Harishanan/Machine-Learning-HPC-/CreateManPage/Screenshot from 2024-03-30 01-08-20.png

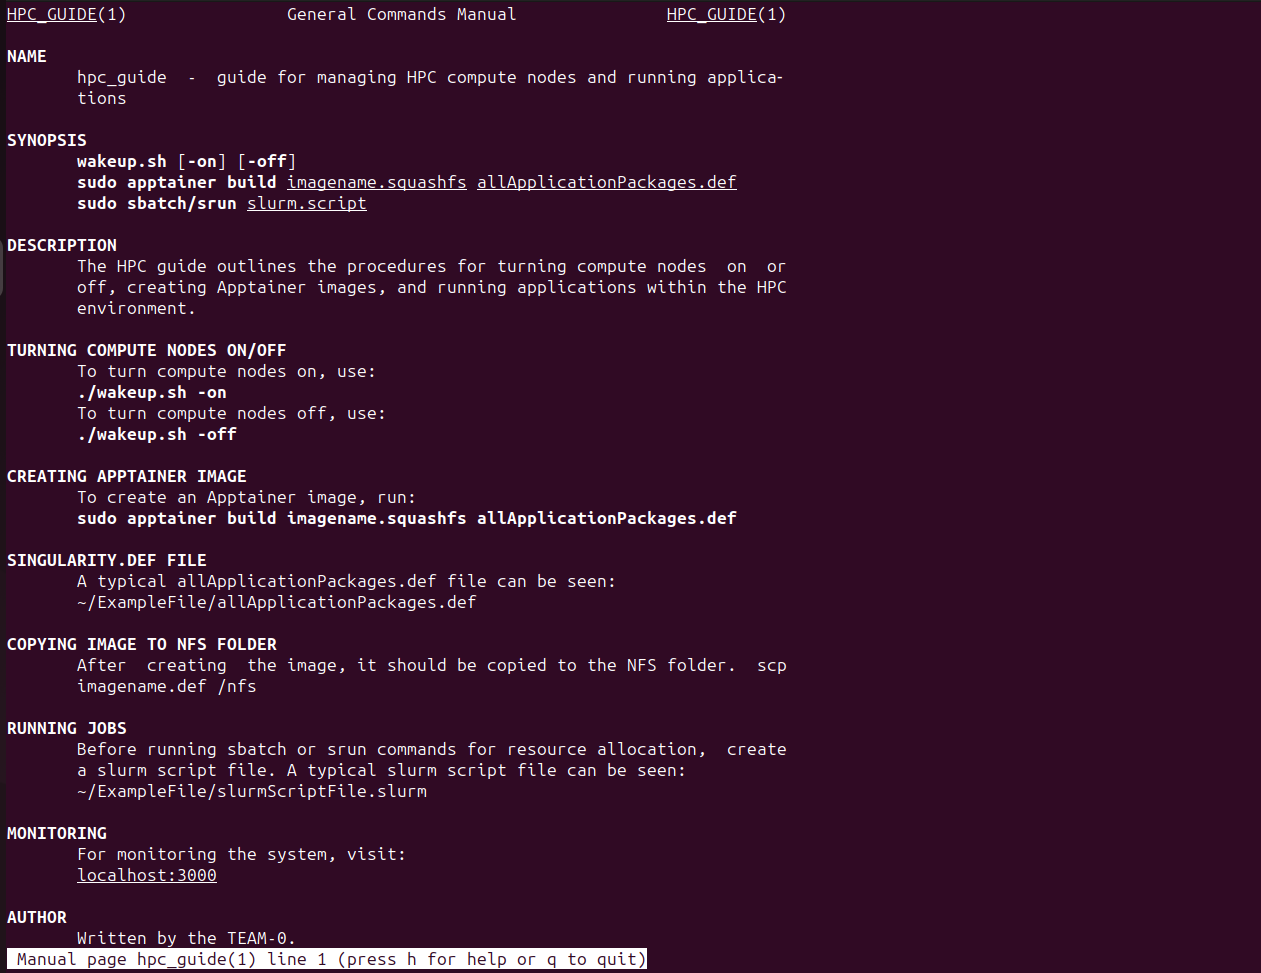
CreateManPage/Screenshot from 2024-03-30 01-08-20.png
