Harishanan/Machine-Learning-HPC-/CreateManPage/Screenshot from 2024-03-30 02-37-32.png

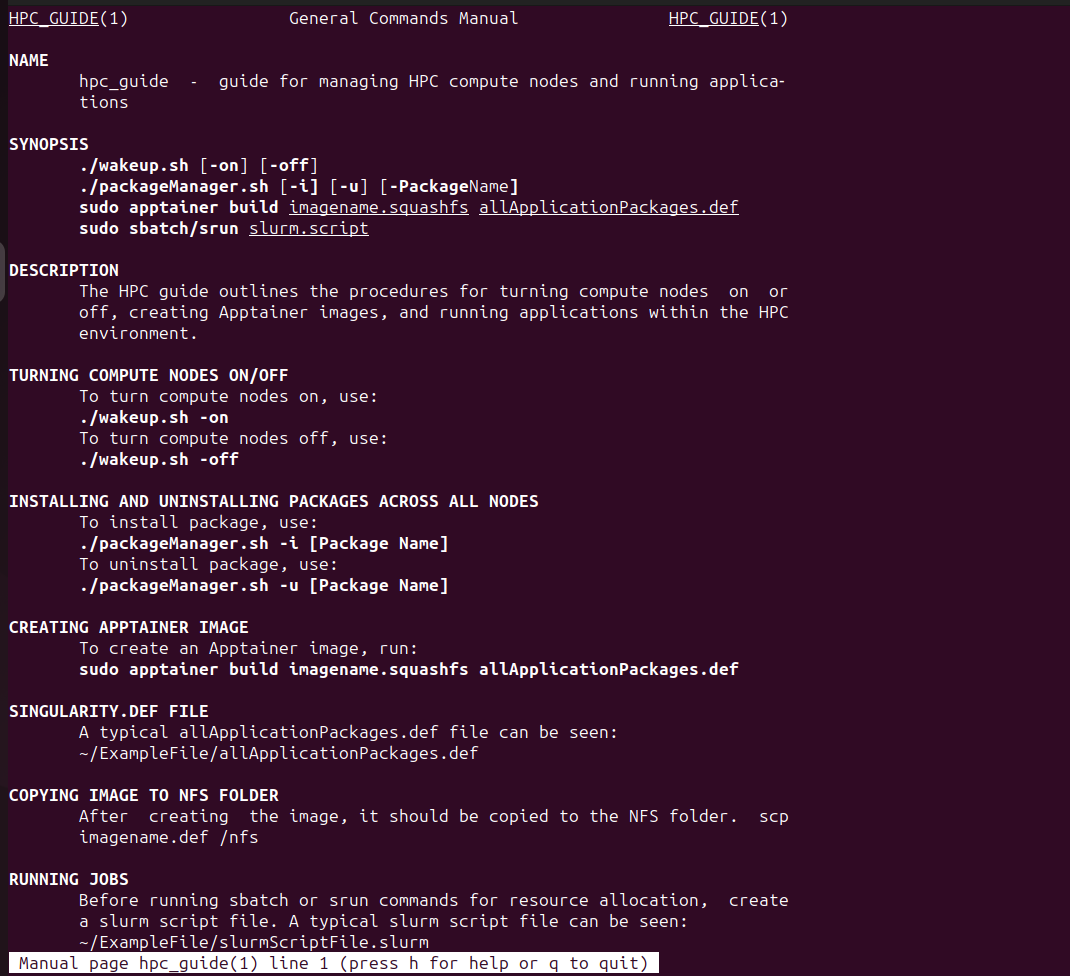
CreateManPage/Screenshot from 2024-03-30 02-37-32.png
