Harishanan/Machine-Learning-HPC-/pictures/image-3.png

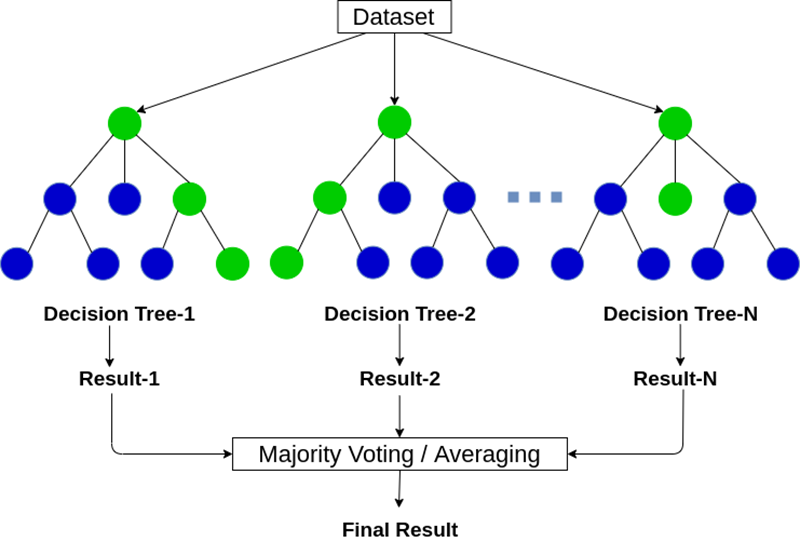
pictures/image-3.png
