Harishanan/Machine-Learning-HPC-/pictures/image-5.png

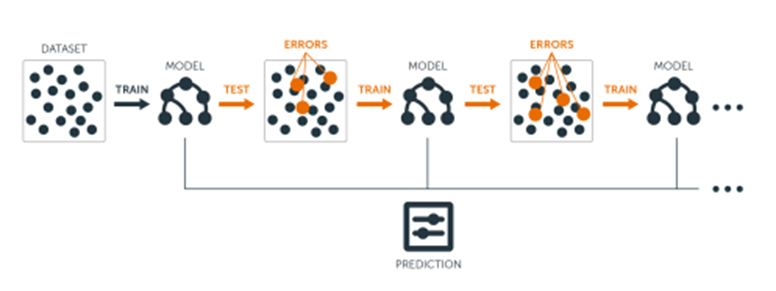
pictures/image-5.png
