Harishanan/Machine-Learning-HPC-/pictures/image-6.png

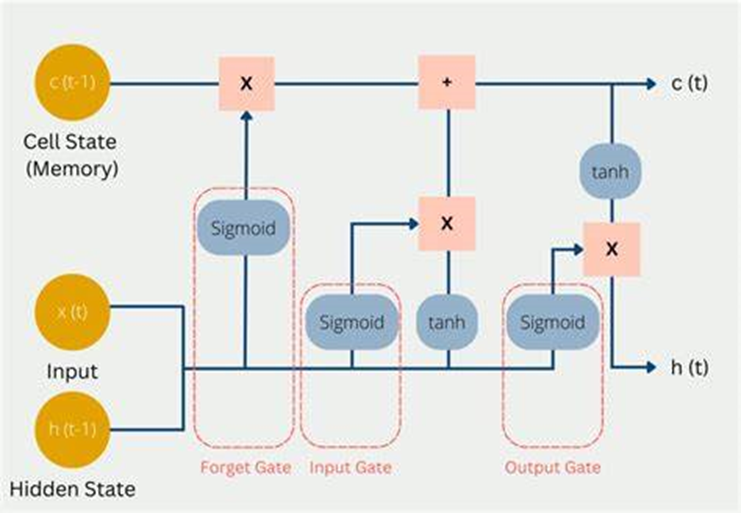
pictures/image-6.png
