Harishanan/Machine-Learning-HPC-/pictures/image-7.png

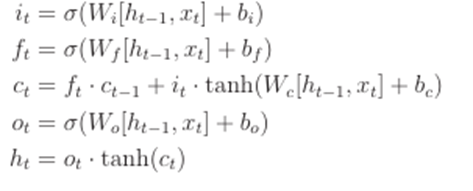
pictures/image-7.png
