Harishanan/Machine-Learning-HPC-/pictures/image-10.png

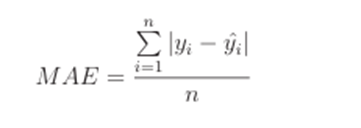
pictures/image-10.png
