Harishanan/Machine-Learning-HPC-/pictures/image-13.png

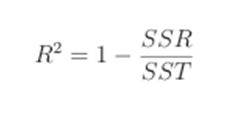
pictures/image-13.png
