Harishanan/Machine-Learning-HPC-/pictures/image-15.png

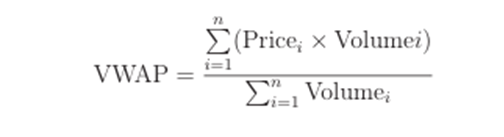
pictures/image-15.png
